freeDSP/freeUSBi/DOCUMENTATION/PICTURES/freeUSBi.png

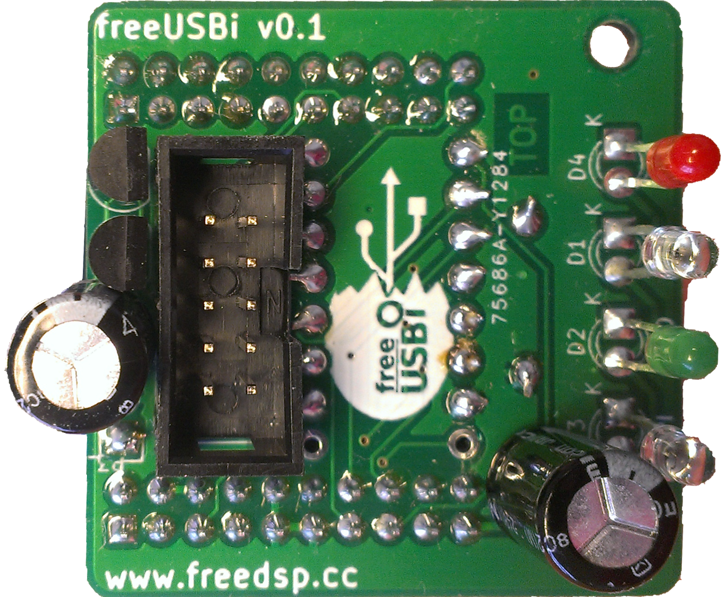
DOCUMENTATION/PICTURES/freeUSBi.png
