freeDSP/freeUSBi/DOCUMENTATION/PICTURES/top.png

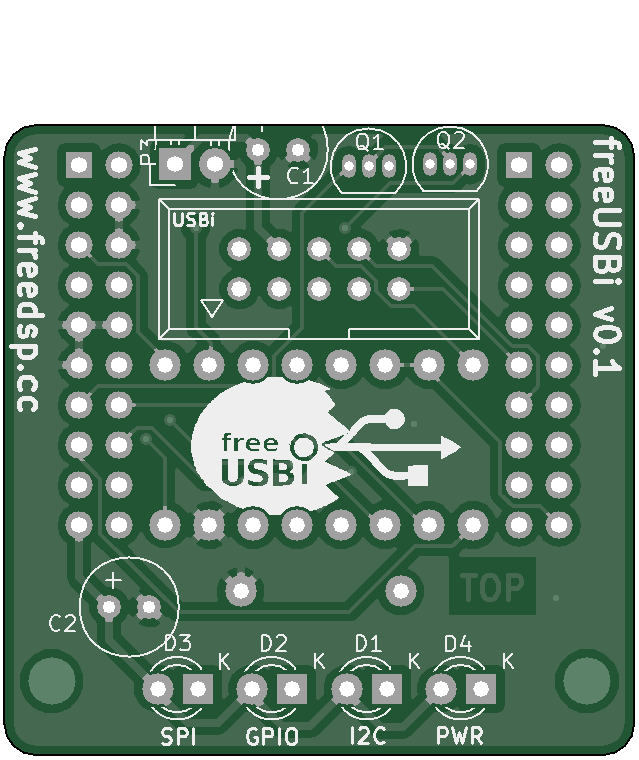
DOCUMENTATION/PICTURES/top.png
