freeDSP/freeUSBi/DOCUMENTATION/PICTURES/Untitled_mono.bmp

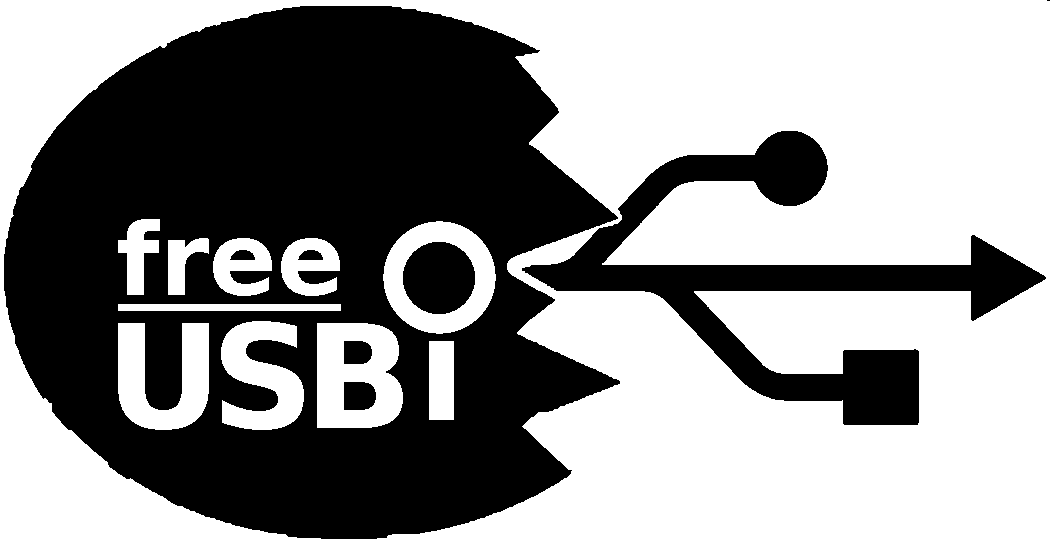
DOCUMENTATION/PICTURES/Untitled_mono.bmp
