freeDSP/freeUSBi/DOCUMENTATION/PICTURES/assemblyprint.png

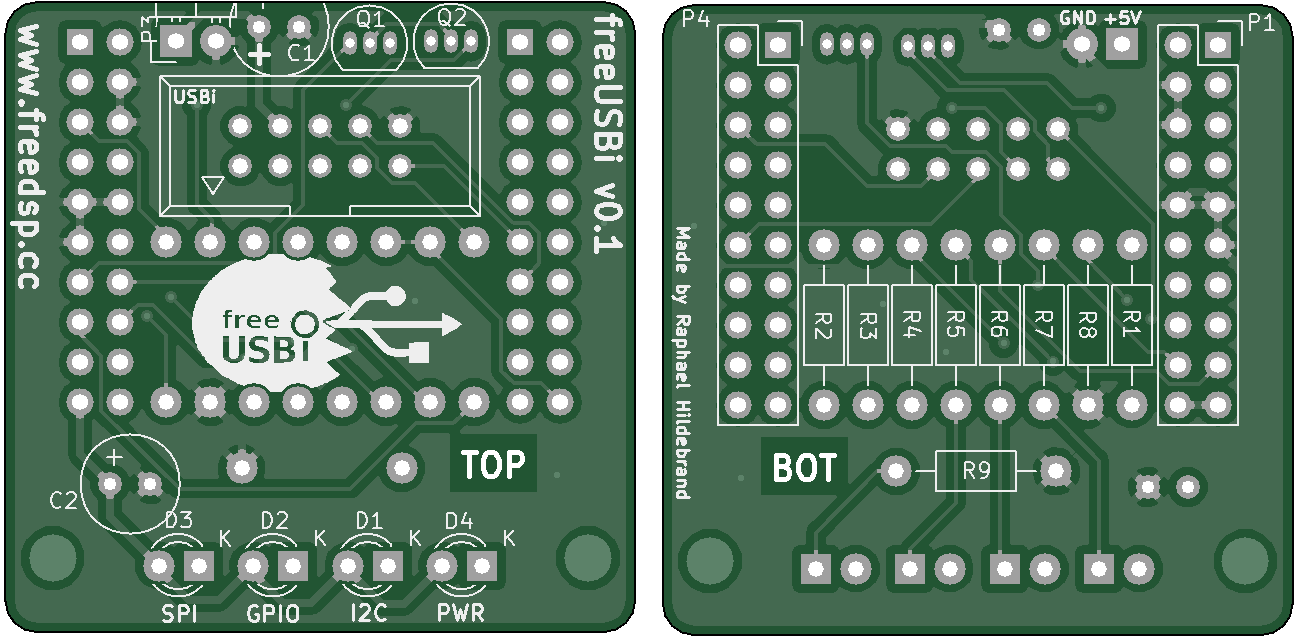
DOCUMENTATION/PICTURES/assemblyprint.png
